robertofelix/geniecom-famiclone-adapter/model3d/phantom/autodeskfusion/case_base.step

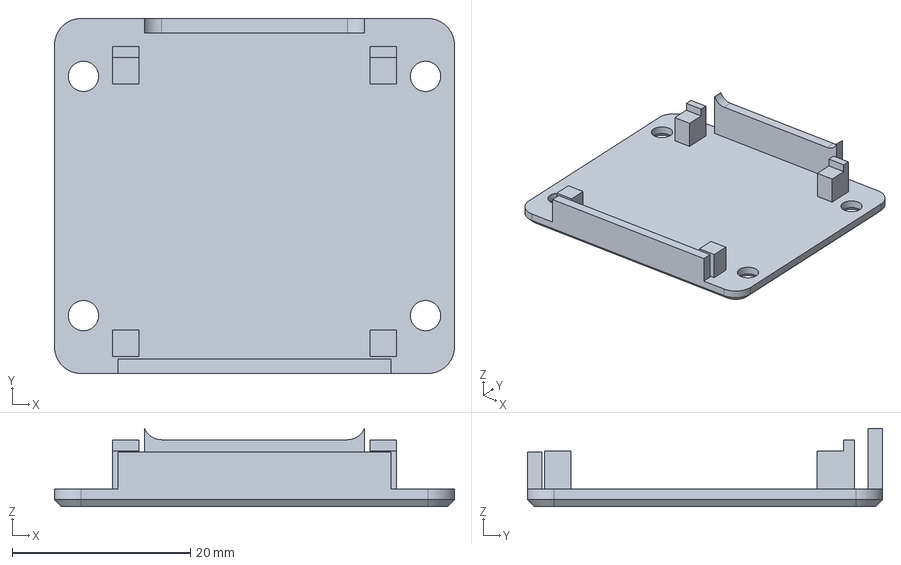
[picture p17: CAD file, 2026-10-08]
model3d/phantom/autodeskfusion/case_base.step
44.9 x 39.9 x 8.79 mm
